cfoge/OPEN_SPECTRE-/fpga/src/analog_side/osc/SinWaveGenerator.vhdl

library IEEE;
use IEEE.STD_LOGIC_1164.ALL;
use IEEE.numeric_std.ALL;
use IEEE.STD_LOGIC_UNSIGNED.ALL;

entity SinWaveGenerator is
    Port (
        clk : in STD_LOGIC;
        reset : in STD_LOGIC;
        freq : in STD_LOGIC_VECTOR(9 downto 0);
        sync_sel : in STD_LOGIC_VECTOR(1 downto 0);
        sync_plus : in STD_LOGIC;
        sync_minus : in STD_LOGIC;
        sin_out : out STD_LOGIC_VECTOR(11 downto 0);
        square_out : out STD_LOGIC
    );
end SinWaveGenerator;

architecture Behavioral of SinWaveGenerator is
    signal counter : STD_LOGIC_VECTOR(9 downto 0) := (others => '0');
    signal phase_accumulator, scaled_freq: STD_LOGIC_VECTOR(11 downto 0) := (others => '0');  -- Use 12 bits for phase accumulator
    signal rom_address : integer range 0 to 180;
    signal sine_table : STD_LOGIC_VECTOR(11 downto 0);
    signal square_i : STD_LOGIC := '0';
    signal sync_edge : STD_LOGIC := '0';
    signal sync_in : STD_LOGIC := '0';

    type ROM is array (0 to 360) of STD_LOGIC_VECTOR(11 downto 0);
    constant sine_rom : ROM := (
"011111111111",
"100001000110",
"100010001101",
"100011010100",
"100100011011",
"100101100010",
"100110101000",
"100111101110",
"101000110011",
"101001110111",
"101010111011",
"101011111101",
"101100111111",
"101110000000",
"101111000000",
"101111111110",
"110000111011",
"110001110111",
"110010110010",
"110011101011",
"110100100010",
"110101011000",
"110110001100",
"110110111111",
"110111110000",
"111000011111",
"111001001100",
"111001110111",
"111010100000",
"111011000110",
"111011101011",
"111100001110",
"111100101110",
"111101001101",
"111101101000",
"111110000010",
"111110011001",
"111110101110",
"111111000001",
"111111010001",
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
    );

begin

    scaled_freq <= freq & "00";

    process(clk, reset, sync_in)
    begin
        if reset = '1' then
            counter <= (others => '0');
            phase_accumulator <= (others => '0');
            sync_edge <= '0';
        elsif rising_edge(clk) then
        
            if sync_sel = "00" then
                sync_in <= '0';
            elsif sync_sel = "01" then
                sync_in <= sync_plus;
            elsif sync_sel = "10" then 
                sync_in <= sync_minus;
            end if;
        
            if sync_in = '1' and sync_edge = '0' then
                sync_edge <= '1';
                counter <= (others => '0');
                phase_accumulator <= (others => '0');
            else
                sync_edge <= sync_in;
                counter <= counter + 1;
                if rom_address > 90 then
                    square_i <= '1';
                    else 
                    square_i <= '0';
                    end if; 
                if counter = scaled_freq then
                    counter <= (others => '0');
                    phase_accumulator <= phase_accumulator + 1;
                    if phase_accumulator = "111111111111" then  -- Adjust the limit for 12 bits
                        phase_accumulator <= (others => '0');
                    end if;
                end if;
            end if;
        end if;
    end process;

    -- ROM lookup
    rom_address <= to_integer(unsigned(phase_accumulator)) mod 180 ;
    

    -- Create the full sine wave using symmetry
    sine_table <= sine_rom(rom_address);
    -- sine_table(11 downto 0) <= sine_table(11 downto 0) & not sine_table(11);  -- Invert the second half

    sin_out <= sine_table;
    square_out <= square_i;

end Behavioral;
