cfoge/OPEN_SPECTRE-/fpga/src/analog_side/ann_matrix/mixer_interface.vhd

----------------------------------------------------------------------------------
-- Company: 
-- Engineer: 
-- 
-- Create Date: 12.09.2023 14:52:58
-- Design Name: 
-- Module Name: mixer_interface - Behavioral
-- Project Name: 
-- Target Devices: 
-- Tool Versions: 
-- Description: 
-- 
-- Dependencies: 
-- 
-- Revision:
-- Revision 0.01 - File Created
-- Additional Comments:
-- 
----------------------------------------------------------------------------------


library IEEE;
use IEEE.STD_LOGIC_1164.ALL;

-- Uncomment the following library declaration if using
-- arithmetic functions with Signed or Unsigned values
--use IEEE.NUMERIC_STD.ALL;

-- Uncomment the following library declaration if instantiating
-- any Xilinx leaf cells in this code.
--library UNISIM;
--use UNISIM.VComponents.all;
library work;
use work.array_pck.all;


entity mixer_interface is

  Port ( 
    clk      :in    STD_LOGIC;
    rst      :in    STD_LOGIC;
    wr       :in    STD_LOGIC;
    out_addr     :in    integer;
    ch_addr      :in    integer;
    gain_in  :in    std_logic_vector(4 downto 0); --gain is 5 bits 32 levels
    mixer_inputs : in array_12(10 downto 0);
    outputs : out array_12(19 downto 0)  

  );
end mixer_interface;

architecture Behavioral of mixer_interface is

signal gain_int : std_logic_vector(3 downto 0) := (others => '0');
signal mixer_gains_0i :  array_5(10 downto 0) := (others => (others => '0'));
signal mixer_gains_1i :  array_5(10 downto 0) := (others => (others => '0'));
signal mixer_gains_2i :  array_5(10 downto 0) := (others => (others => '0'));
signal mixer_gains_3i :  array_5(10 downto 0) := (others => (others => '0'));
signal mixer_gains_4i :  array_5(10 downto 0) := (others => (others => '0'));
signal mixer_gains_5i :  array_5(10 downto 0) := (others => (others => '0'));
signal mixer_gains_6i :  array_5(10 downto 0) := (others => (others => '0'));
signal mixer_gains_7i :  array_5(10 downto 0) := (others => (others => '0'));
signal mixer_gains_8i :  array_5(10 downto 0) := (others => (others => '0'));
signal mixer_gains_9i :  array_5(10 downto 0) := (others => (others => '0'));
signal mixer_gains_10i :  array_5(10 downto 0) := (others => (others => '0'));
signal mixer_gains_11i :  array_5(10 downto 0) := (others => (others => '0'));
signal mixer_gains_12i :  array_5(10 downto 0) := (others => (others => '0'));
signal mixer_gains_13i :  array_5(10 downto 0) := (others => (others => '0'));
signal mixer_gains_14i :  array_5(10 downto 0) := (others => (others => '0'));
signal mixer_gains_15i :  array_5(10 downto 0) := (others => (others => '0'));
signal mixer_gains_16i :  array_5(10 downto 0) := (others => (others => '0'));
signal mixer_gains_17i :  array_5(10 downto 0) := (others => (others => '0'));
signal mixer_gains_18i :  array_5(10 downto 0) := (others => (others => '0'));
signal mixer_gains_19i :  array_5(10 downto 0) := (others => (others => '0'));

begin

process (clk) is
begin
    if rising_edge (clk) then
        if wr = '1' then
           case out_addr is
            when 0 =>
                mixer_gains_0i(ch_addr) <= gain_in;
            when 1 =>
                mixer_gains_1i(ch_addr) <= gain_in;
            when 2 =>
                mixer_gains_2i(ch_addr) <= gain_in;
            when 3 =>
                mixer_gains_3i(ch_addr) <= gain_in;
            when 4 =>
                mixer_gains_4i(ch_addr) <= gain_in;
            when 5 =>
                mixer_gains_5i(ch_addr) <= gain_in;
            when 6 =>
                mixer_gains_6i(ch_addr) <= gain_in;
            when 7 =>
                mixer_gains_7i(ch_addr) <= gain_in;
            when 8 =>
                mixer_gains_8i(ch_addr) <= gain_in;
            when 9 =>
                mixer_gains_9i(ch_addr) <= gain_in;
            when 10 =>
                mixer_gains_10i(ch_addr) <= gain_in;
            when 11 =>
                mixer_gains_11i(ch_addr) <= gain_in;
            when 12 =>
                mixer_gains_12i(ch_addr) <= gain_in;
            when 13 =>
                mixer_gains_13i(ch_addr) <= gain_in;
            when 14 =>
                mixer_gains_14i(ch_addr) <= gain_in;
            when 15 =>
                mixer_gains_15i(ch_addr) <= gain_in;
            when 16 =>
                mixer_gains_16i(ch_addr) <= gain_in;
            when 17 =>
                mixer_gains_17i(ch_addr) <= gain_in;
            when 18 =>
                mixer_gains_18i(ch_addr) <= gain_in;
            when 19 =>
                mixer_gains_19i(ch_addr) <= gain_in;
            when others => -- 'U', 'X', '-', etc.
                mixer_gains_19i(ch_addr) <= (others => '0');
        end case;
        
        elsif rst = '1' then
             mixer_gains_0i <= (others => (others => '0'));
             mixer_gains_1i <= (others => (others => '0'));
             mixer_gains_2i <= (others => (others => '0'));
             mixer_gains_3i <= (others => (others => '0'));
             mixer_gains_4i <= (others => (others => '0'));
             mixer_gains_5i <= (others => (others => '0'));
             mixer_gains_6i <= (others => (others => '0'));
             mixer_gains_7i <= (others => (others => '0'));
             mixer_gains_8i <= (others => (others => '0'));
             mixer_gains_9i <= (others => (others => '0'));
             mixer_gains_10i <= (others => (others => '0'));
             mixer_gains_11i <= (others => (others => '0'));
             mixer_gains_12i <= (others => (others => '0'));
             mixer_gains_13i <= (others => (others => '0'));
             mixer_gains_14i <= (others => (others => '0'));
             mixer_gains_15i <= (others => (others => '0'));
             mixer_gains_16i <= (others => (others => '0'));
             mixer_gains_17i <= (others => (others => '0'));
             mixer_gains_18i <= (others => (others => '0'));
             mixer_gains_19i <= (others => (others => '0'));
       end if;
    
    end if;
end process;

analog_matrix : entity work.analog_matrix
    Port map (
         clk => clk,
         reset => rst,
         mixer_inputs => mixer_inputs,
         mixer_gains_0 => mixer_gains_0i,
         mixer_gains_1 => mixer_gains_1i,
         mixer_gains_2 => mixer_gains_2i,
         mixer_gains_3 => mixer_gains_3i,
         mixer_gains_4 => mixer_gains_4i,
         mixer_gains_5 => mixer_gains_5i,
         mixer_gains_6 => mixer_gains_6i,
         mixer_gains_7 => mixer_gains_7i,
         mixer_gains_8 => mixer_gains_8i,
         mixer_gains_9 => mixer_gains_9i,
         mixer_gains_10 => mixer_gains_10i,
         mixer_gains_11 => mixer_gains_11i,
         mixer_gains_12 => mixer_gains_12i,
         mixer_gains_13 => mixer_gains_13i,
         mixer_gains_14 => mixer_gains_14i,
         mixer_gains_15 => mixer_gains_15i,
         mixer_gains_16 => mixer_gains_16i,
         mixer_gains_17 => mixer_gains_17i,
         mixer_gains_18 => mixer_gains_18i,
         mixer_gains_19 => mixer_gains_19i,
        outputs => outputs
    );


end Behavioral;
