cfoge/OPEN_SPECTRE-/src/video_output/ycrcb2rgb_tb.v

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
//  CVS Log
//
//  $Id: testbench.v,v 1.1.1.1 2002-03-26 07:25:07 rherveille Exp $
//
//  $Date: 2002-03-26 07:25:07 $
//  $Revision: 1.1.1.1 $
//  $Author: rherveille $
//  $Locker:  $
//  $State: Exp $
//
// Change History:
//               $Log: not supported by cvs2svn $


`timescale 1ns/10ps

module testbench();

	parameter emargin = 1; // we allow a small (rounding) error
	parameter debug = 0;
	parameter y_runlength = 50;
	parameter cr_runlength = 50;
	parameter cb_runlength = 50;

	// variables
	reg clk;
	reg ena;

	reg  [9:0] y [3:0];
	reg  [9:0] cr [3:0];
	reg  [9:0] cb [3:0];

	wire [9:0] r, g, b;

	integer yc, crc, cbc;

	integer mr, mg, mb;
	integer ir, ig, ib;

	//
	// module body
	//

	// hookup modules
	ycrcb2rgb dut (
		.clk(clk),
		.ena(ena),
		.y(y[0]),
		.cr(cr[0]),
		.cb(cb[0]),
		.r(r),
		.g(g),
		.b(b)
	);

	always #5 clk <= ~clk;

	initial
	begin
		clk = 0;
		ena = 1;
	
		y[0]  = 0;
		cr[0] = 0;
		cb[0] = 0;

		$display ("\n *** Color Space Converter testbench started ***\n");

		for (cbc = 0; cbc <= cb_runlength; cbc = cbc +1)
		for (crc = 0; crc <= cr_runlength; crc = crc +1)
		for (yc  = 0; yc  <= y_runlength;  yc  = yc  +1)
		begin
			@(posedge clk);
			#1;

			y[0]  = yc;
			cr[0] = crc;
			cb[0] = cbc;

			if (debug)
				$display("y[0] = %d, cr[0] = %d, cb[0] = %d", y[0], cr[0], cb[0]);
		end

			$display ("\n *** Color Space Converter testbench ended ***\n");
			$stop;
	end


	integer n;
	always@(posedge clk)
	begin
		for (n = 0; n < 3; n = n +1)
		begin
			y[n +1]  <= #1 y[n];
			cr[n +1] <= #1 cr[n];
			cb[n +1] <= #1 cb[n];
		end
	end

	always@(y[3] or cr[3] or cb[3])
	begin
		mr  = (y[3] * 1000) + (1403 * cr[3]);
		if (mr < 0)
			mr = 0;

		mr = mr /1000;
		if (mr > 1023)
			mr = 1023;

		mg = (y[3] * 1000) - ( (344 * cb[3]) + (714 * cr[3]) );
		if (mg < 0)
			mg = 0;

		mg = mg /1000;
		if (mg > 1023)
			mg = 1023;

		mb = (y[3] * 1000) + (1770 * cb[3]);
		if (mb < 0)
			mb = 0;

		mb = mb /1000;
		if (mb > 1023)
			mb = 1023;
	end

	always@(posedge clk)
	begin
		// check RGB results
		ir = r;
		if ( ( ir < mr - emargin) || (ir > mr + emargin) )
			$display("R-value error. Received %d, expected %d. Y = %d, Cr = %d, Cb = %d", ir, mr, y[3], cr[3], cb[3]);

		ig = g;
		if ( ( ig < mg - emargin) || (ig > mg + emargin) )
			$display("G-value error. Received %d, expected %d. Y = %d, Cr = %d, Cb = %d", ig, mg, y[3], cr[3], cb[3]);

		ib = b;
		if ( ( ib < mb - emargin) || (ib > mb + emargin) )
			$display("B-value error. Received %d, expected %d. Y = %d, Cr = %d, Cb = %d", ib, mb, y[3], cr[3], cb[3]);
	end

endmodule
